Acidpix/Pony-Card-WRS4i2o/Hardware/REV-B/3d/QSG5032.step

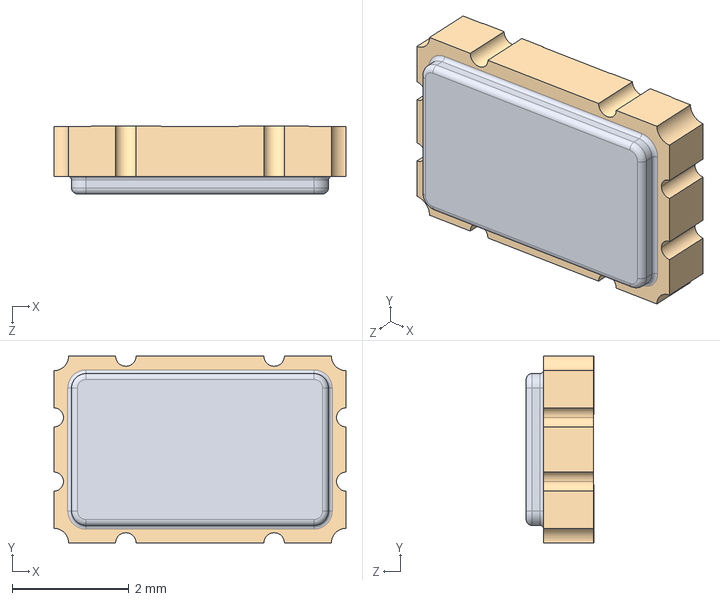
[picture p17: CAD file, 2024-01-12]
Hardware/REV-B/3d/QSG5032.step
5.00 x 3.20 x 1.16 mm
