Acidpix/Pony-Card-WRS4i2o/Hardware/REV-B/3d/TEConnectivity -ORWH-SH-124D1F000.stp

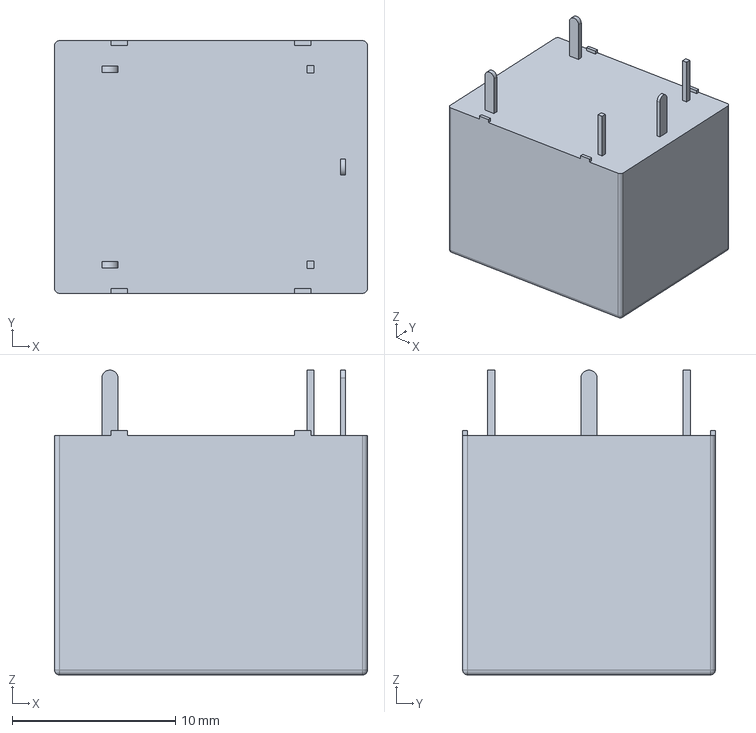
[picture p18: CAD file, 2024-01-12]
Hardware/REV-B/3d/TEConnectivity -ORWH-SH-124D1F000.stp
19.2 x 15.5 x 18.7 mm
