Acidpix/Pony-Card-WRS4i2o/Hardware/REV-B/3d/QFN32_5x5.step

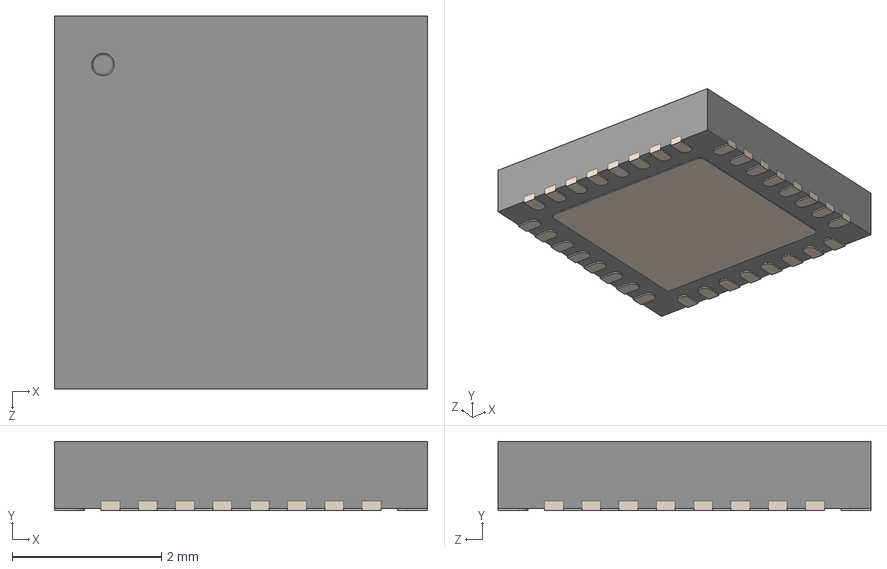
[picture p19: CAD file, 2024-01-12]
Hardware/REV-B/3d/QFN32_5x5.step
5.00 x 0.93 x 5.00 mm
