Acidpix/Pony-Card-WRS4i2o/Hardware/REV-B/3d/BH-10__64.step

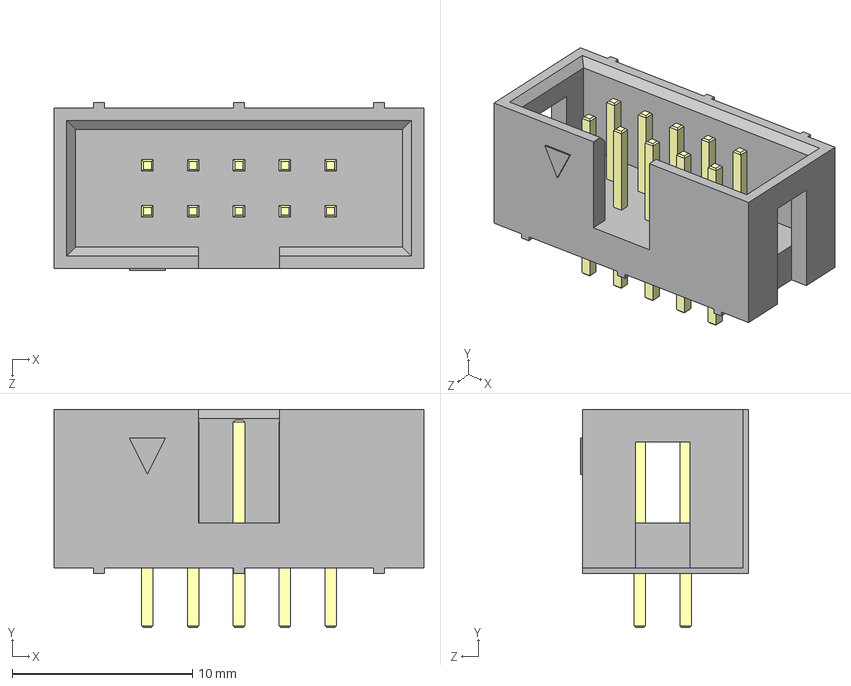
[picture p20: CAD file, 2024-01-12]
Hardware/REV-B/3d/BH-10__64.step
20.5 x 12.1 x 9.30 mm
