Acidpix/Pony-Card-WRS4i2o/Hardware/REV-B/3d/esp-wroom-32.step

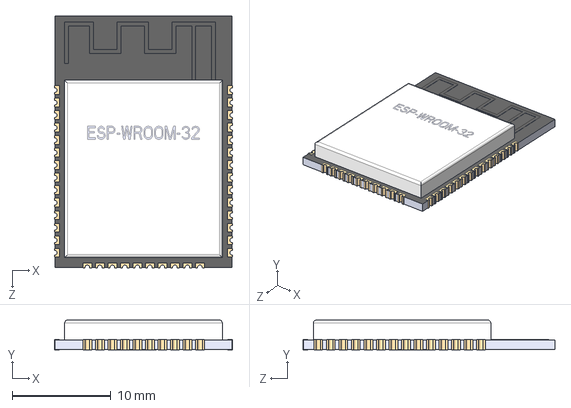
[picture p21: CAD file, 2024-01-12]
Hardware/REV-B/3d/esp-wroom-32.step
18.1 x 3.04 x 25.5 mm
