Acidpix/Pony-Card-WRS4i2o/Hardware/REV-B/3d/User Library-GP1UE26.STEP

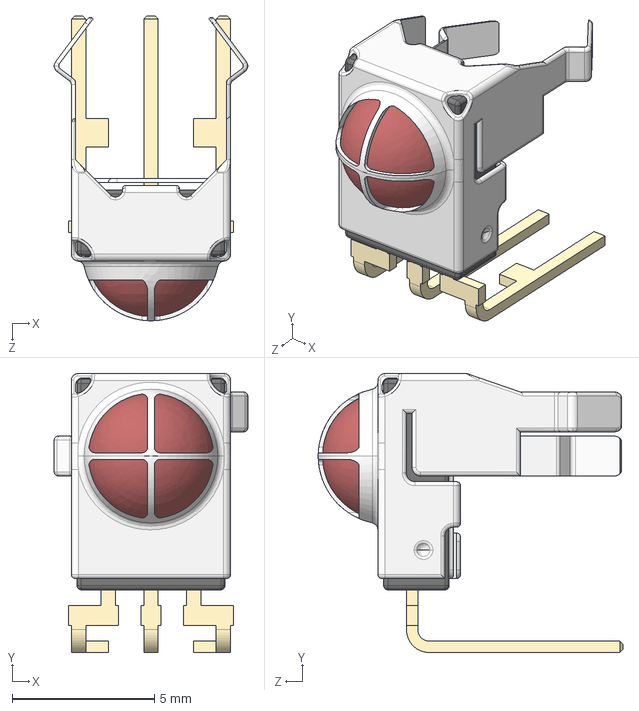
[picture p22: CAD file, 2024-01-12]
Hardware/REV-B/3d/User Library-GP1UE26.STEP
6.80 x 9.80 x 10.7 mm
