Acidpix/Pony-Card-WRS4i2o/Hardware/REV-B/3d/SOT-23.step

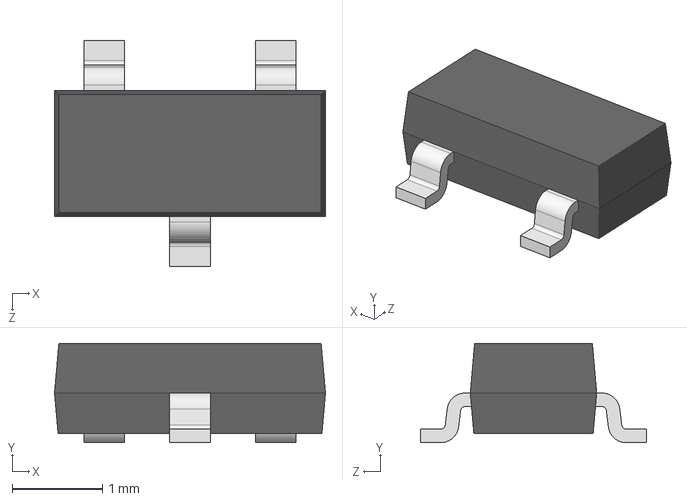
[picture p23: CAD file, 2024-01-12]
Hardware/REV-B/3d/SOT-23.step
3.00 x 1.10 x 2.50 mm
