Acidpix/Pony-Card-WRS4i2o/Hardware/REV-B/3d/usb_micro_4p.stp

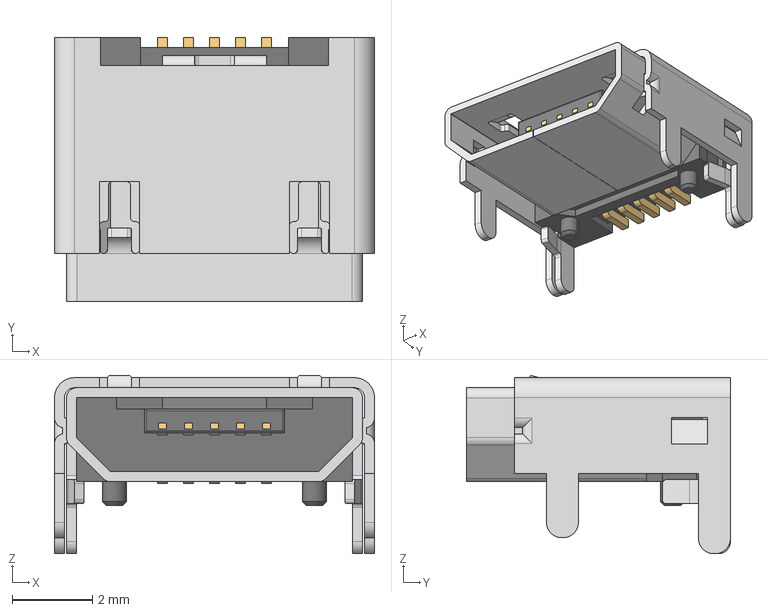
[picture p24: CAD file, 2024-01-12]
Hardware/REV-B/3d/usb_micro_4p.stp
8.00 x 6.60 x 4.46 mm
